jsware/t800-hk/docs/assets/images/base-back.jpg

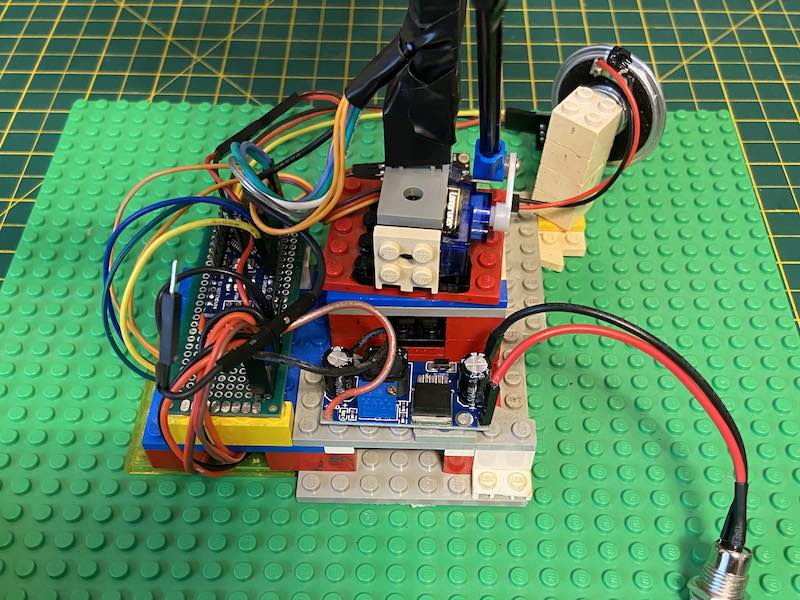
docs/assets/images/base-back.jpg
