jsware/t800-hk/docs/assets/images/base-cabling.jpg

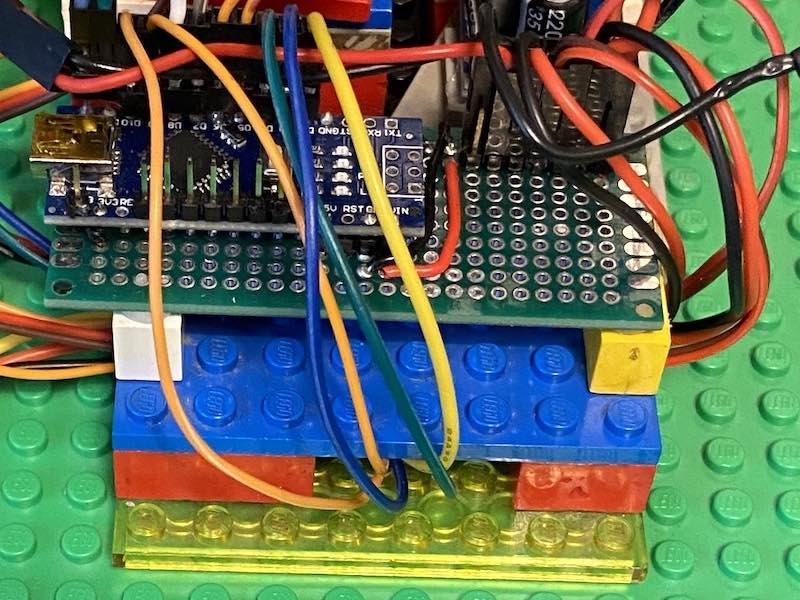
docs/assets/images/base-cabling.jpg
