jsware/t800-hk/docs/assets/images/base-closeup.jpg

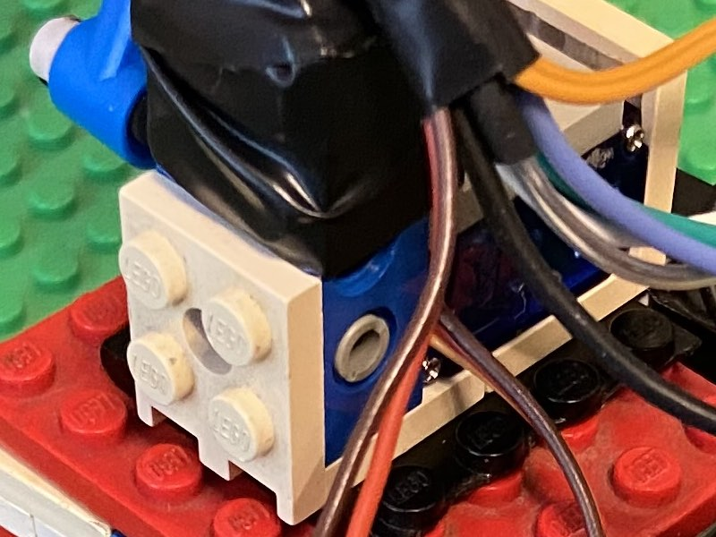
docs/assets/images/base-closeup.jpg
