jsware/t800-hk/docs/assets/images/base-front.jpg

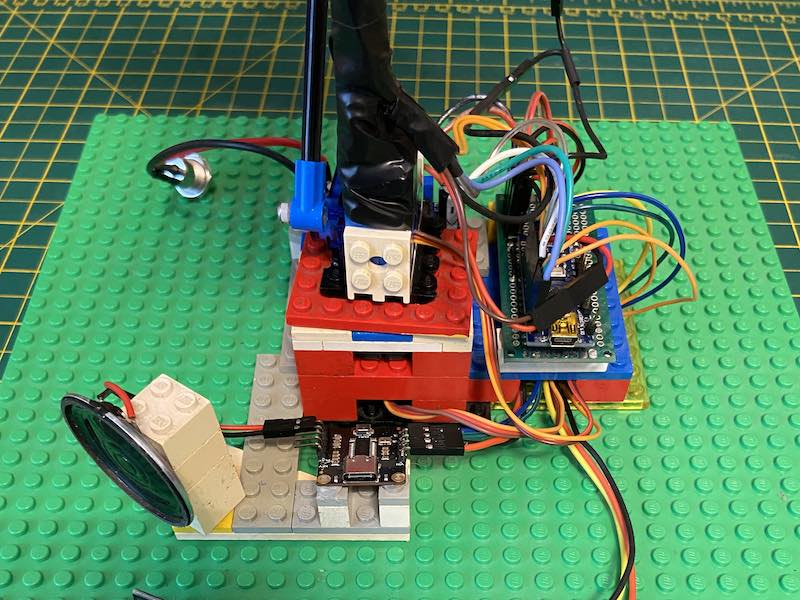
docs/assets/images/base-front.jpg
