jsware/t800-hk/docs/assets/images/base-left.jpg

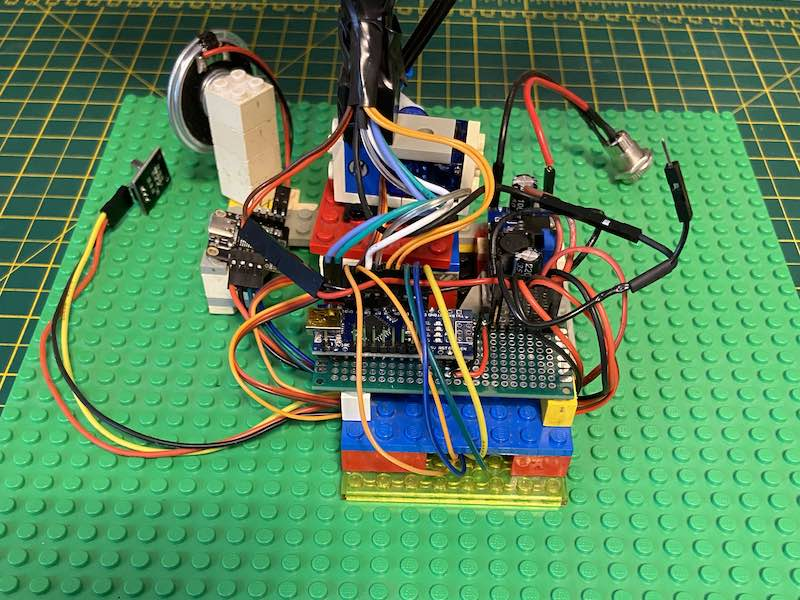
docs/assets/images/base-left.jpg
