jsware/t800-hk/docs/assets/images/base-lights.jpg

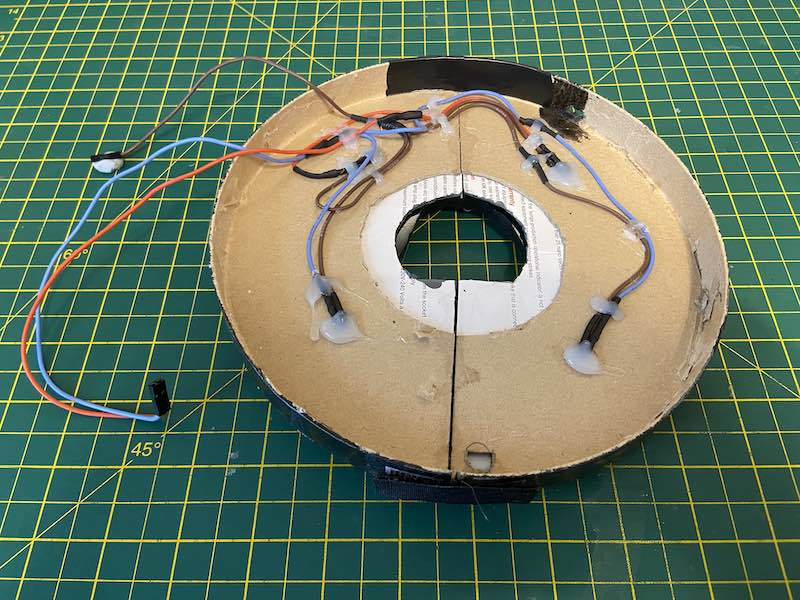
docs/assets/images/base-lights.jpg
