jsware/t800-hk/docs/assets/images/base-mold.jpg

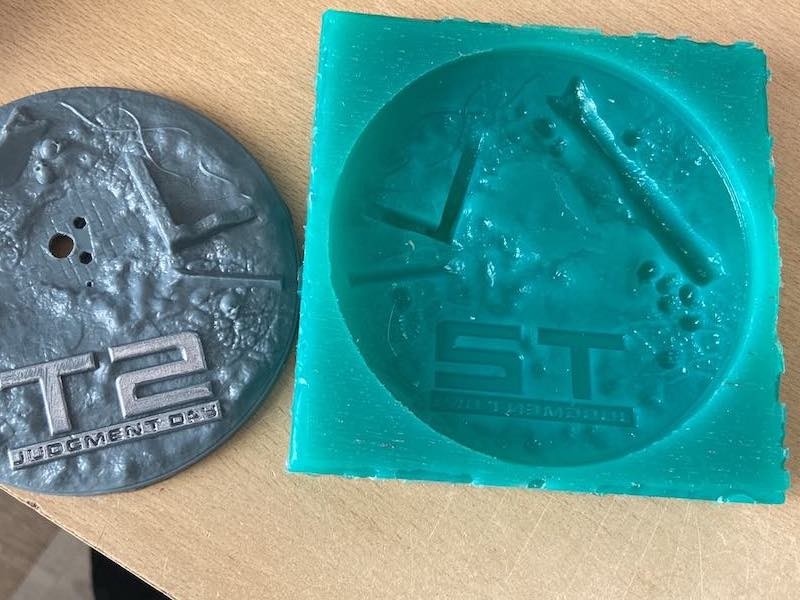
docs/assets/images/base-mold.jpg
