jsware/t800-hk/docs/assets/images/base-open1.jpg

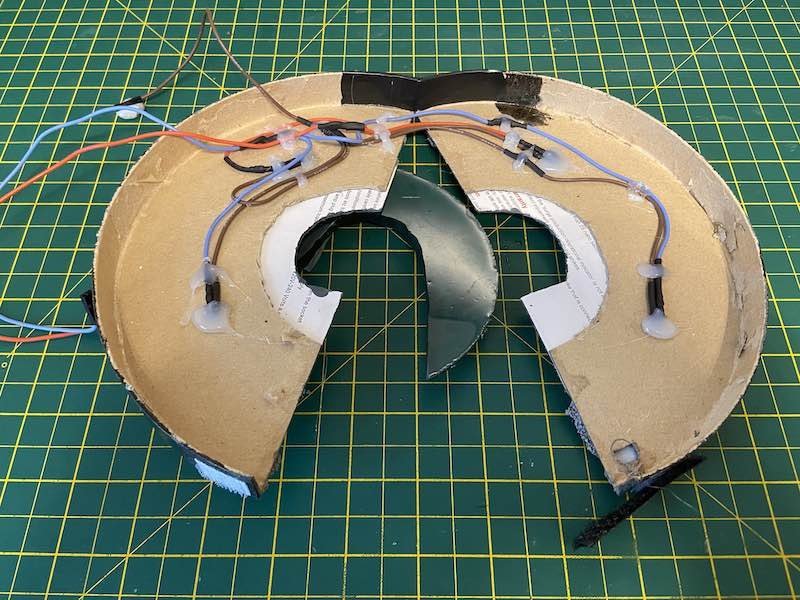
docs/assets/images/base-open1.jpg
