jsware/t800-hk/docs/assets/images/base-open2.jpg

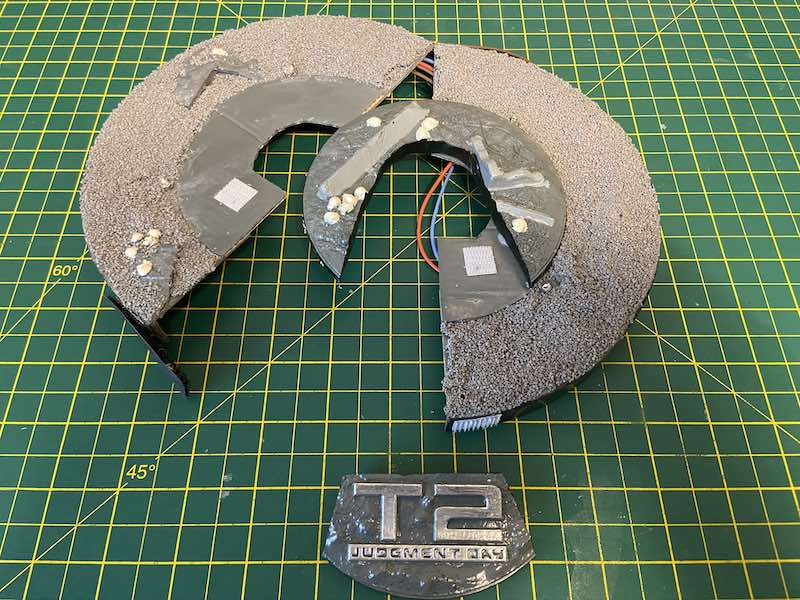
docs/assets/images/base-open2.jpg
