jsware/t800-hk/docs/assets/images/base-right.jpg

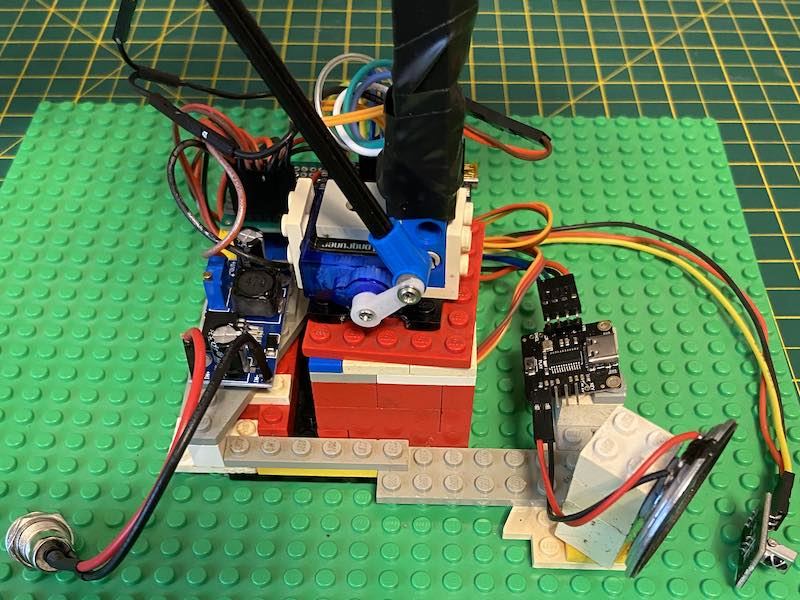
docs/assets/images/base-right.jpg
