jsware/t800-hk/docs/assets/images/base-top.jpg

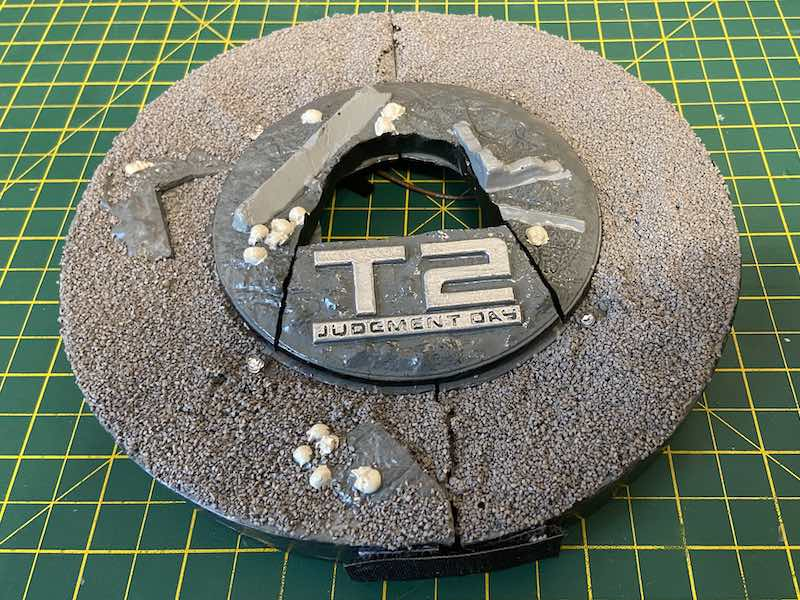
docs/assets/images/base-top.jpg
