jsware/t800-hk/docs/assets/images/chrome.jpg

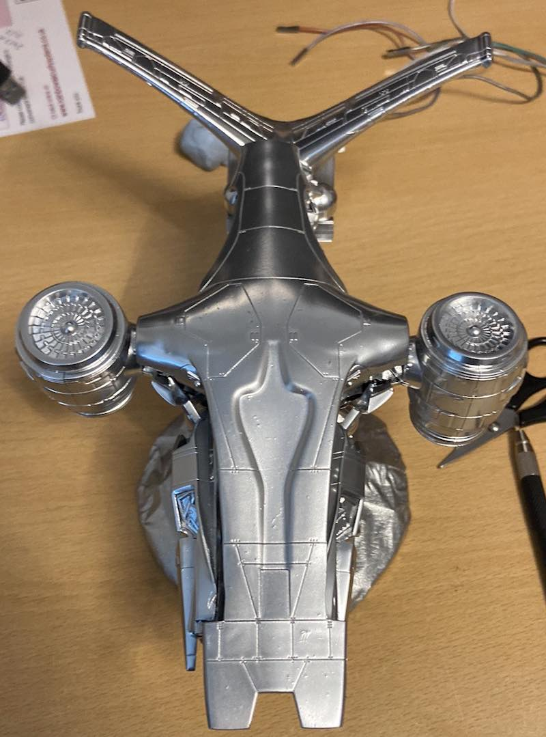
docs/assets/images/chrome.jpg
