jsware/t800-hk/docs/assets/images/hk-cover1.jpg

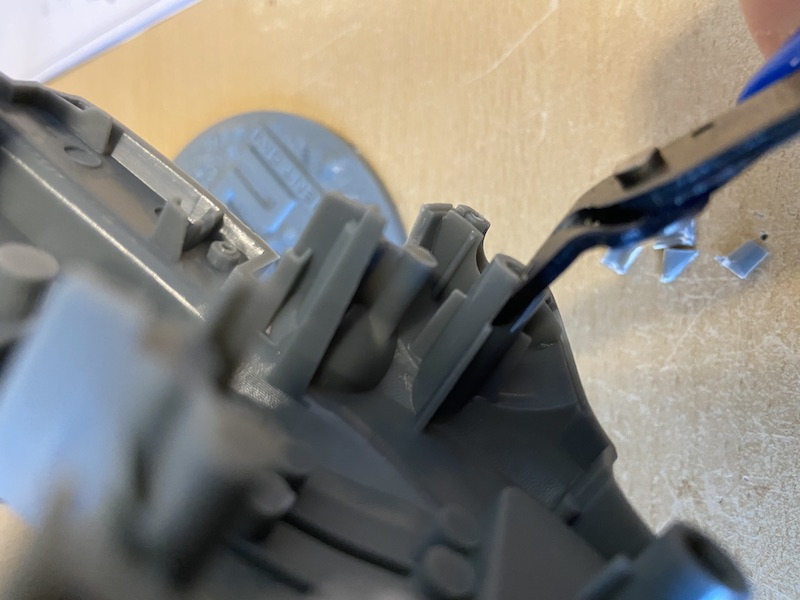
docs/assets/images/hk-cover1.jpg
