jsware/t800-hk/docs/assets/images/hk-lights.jpg

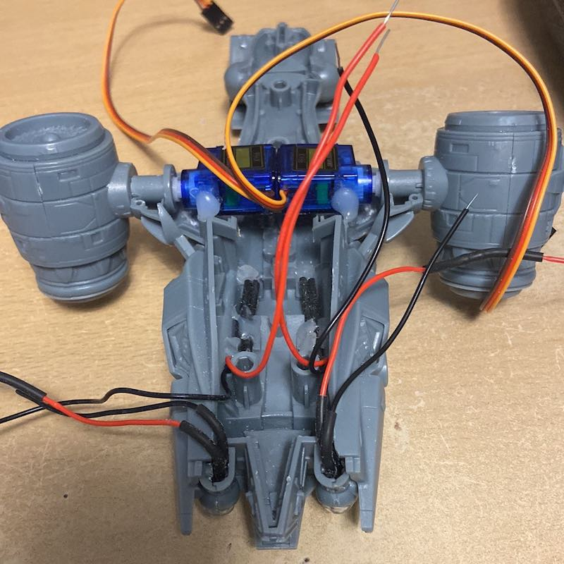
docs/assets/images/hk-lights.jpg
