jsware/t800-hk/docs/assets/images/hk-thrust.jpg

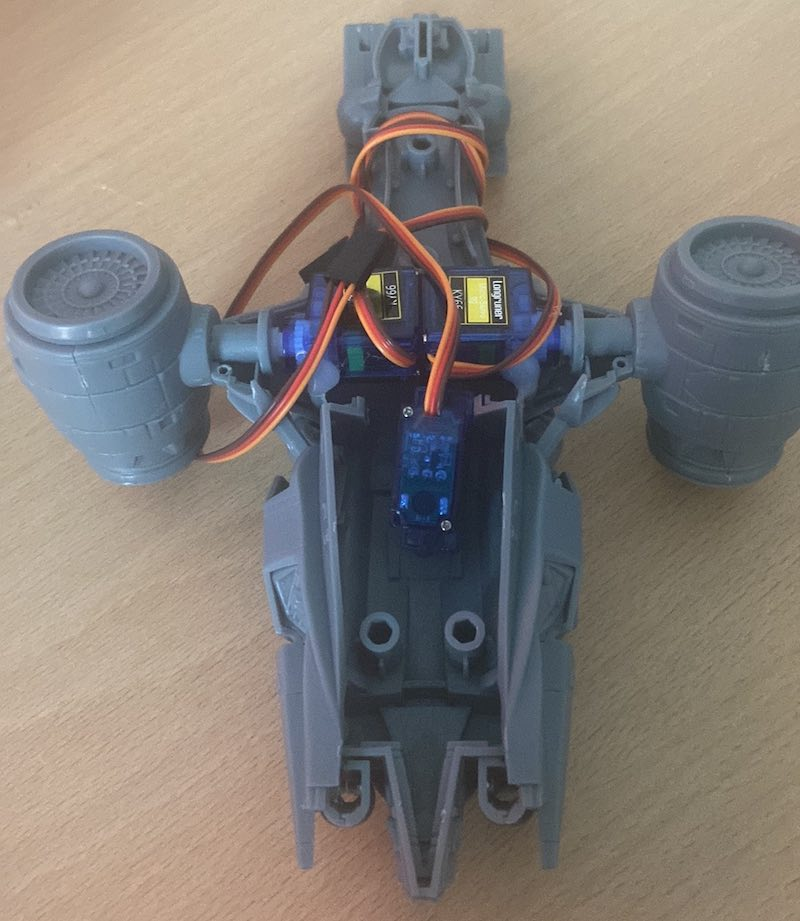
docs/assets/images/hk-thrust.jpg
