jsware/t800-hk/docs/assets/images/hk-underside.jpg

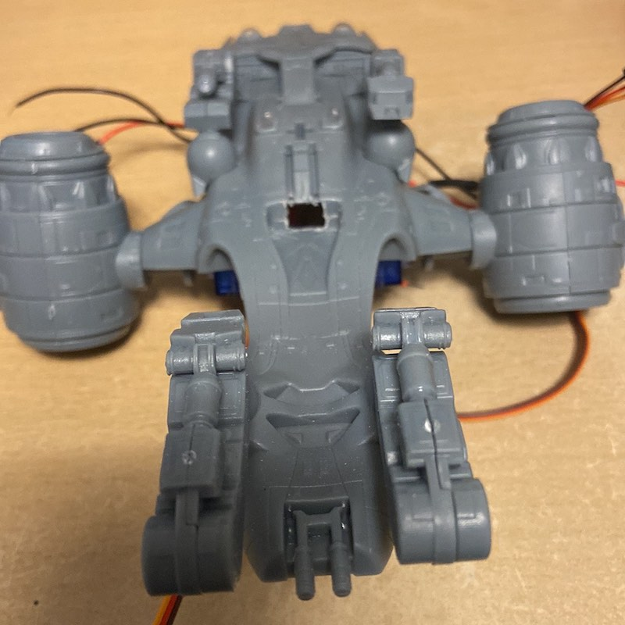
docs/assets/images/hk-underside.jpg
