jsware/t800-hk/docs/assets/images/plasma-gun.jpg

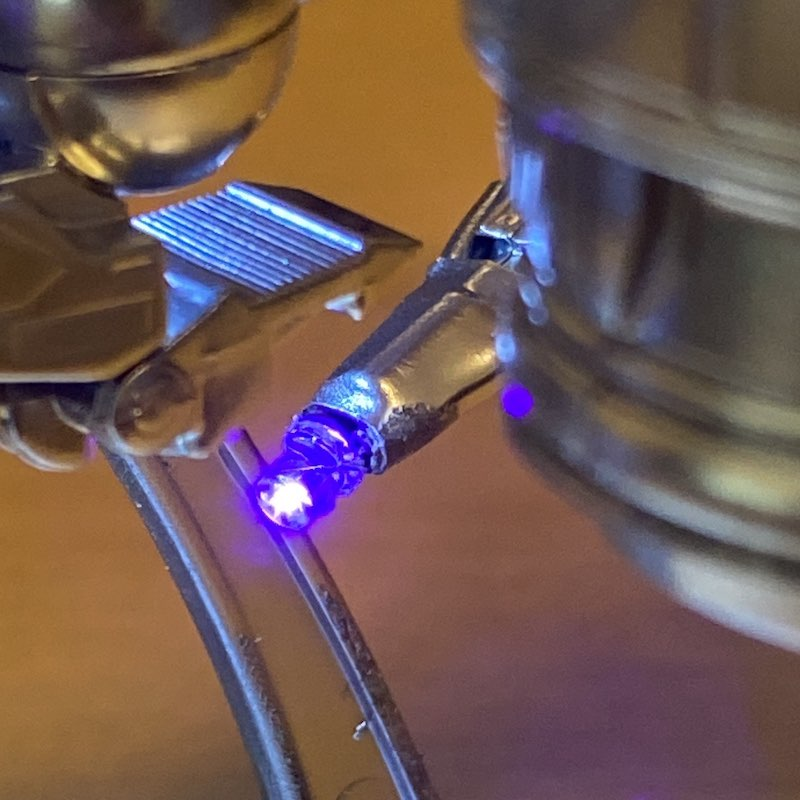
docs/assets/images/plasma-gun.jpg
