jsware/t800-hk/docs/assets/images/search-fire.jpg

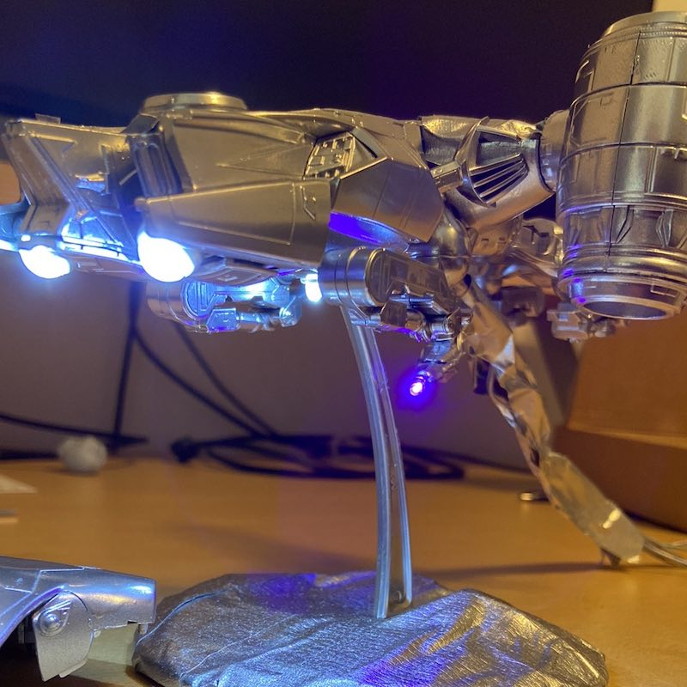
docs/assets/images/search-fire.jpg
