jsware/t800-hk/docs/assets/images/tail-lights.jpg

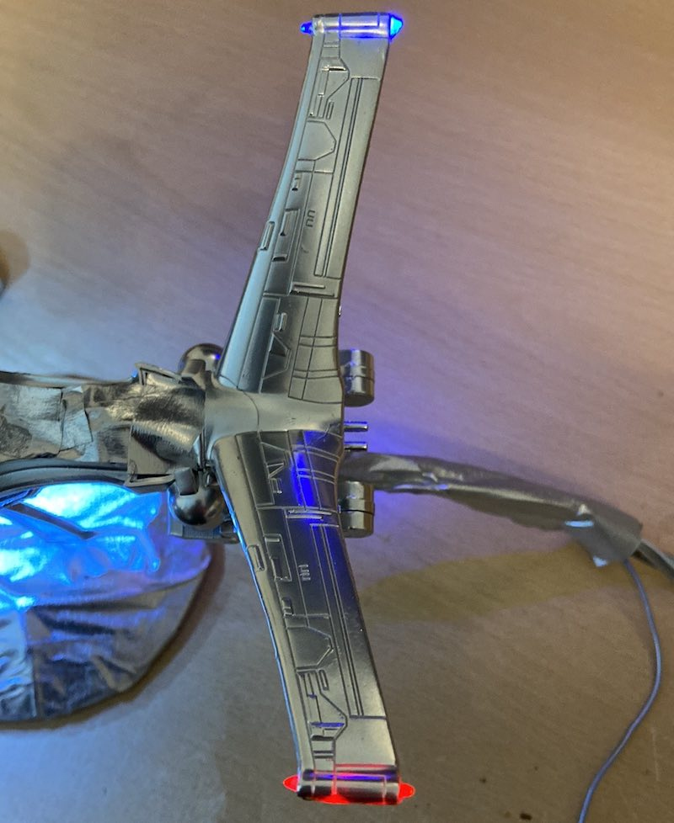
docs/assets/images/tail-lights.jpg
