jsware/t800-hk/docs/assets/images/wired-up.jpg

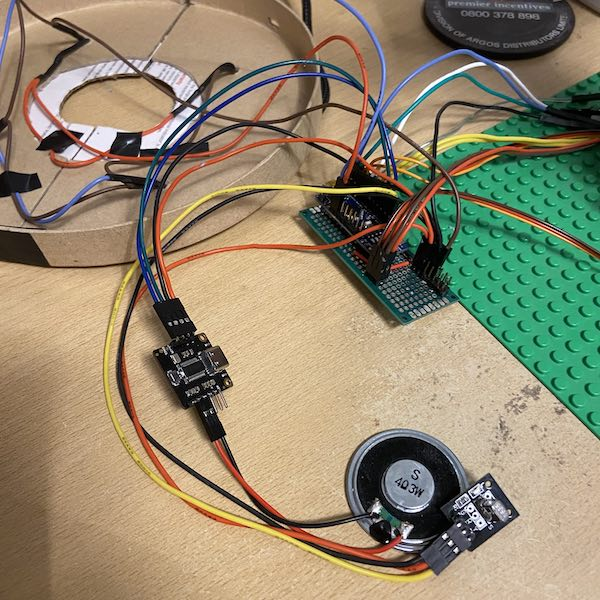
docs/assets/images/wired-up.jpg
