jsware/t800-hk/include/ahkctrl.h

/**
 * @file ahkctrl.h
 * @author John Scott
 * @brief Class to control the Aerial HK.
 * @version 1.0
 * @date 2022-04-25
 * 
 * @copyright Copyright (c) 2022 John Scott.
 */
#ifndef INCLUDED_AHKCTRL_H
#define INCLUDED_AHKCTRL_H

void setupAHKCtrl(); ///< Setup controller.
void loopAHKCtrl(); ///< Handle AHK Controls.

#endif /* INCLUDED_AHKCTRL_H */
